Dynatrace/ufo/3dprint/ufo case sketch.png

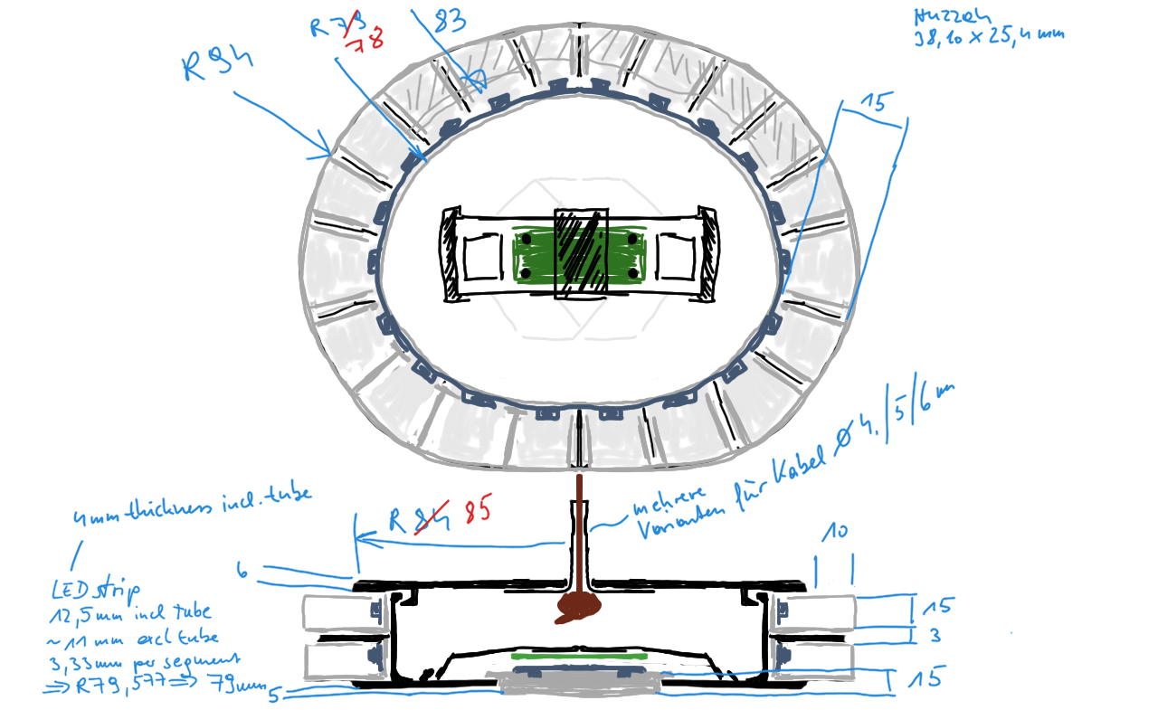
3dprint/ufo case sketch.png
