Dynatrace/ufo/howto/install neopixel library.png

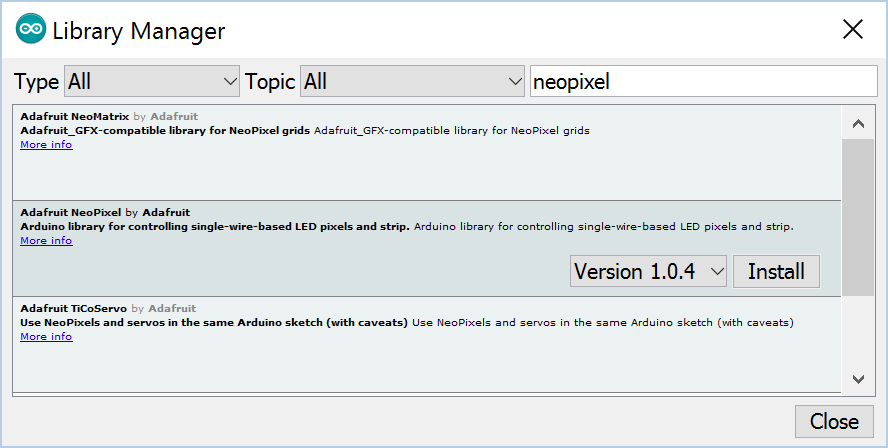
howto/install neopixel library.png
