Dynatrace/ufo/story/printed ufo lowres.png

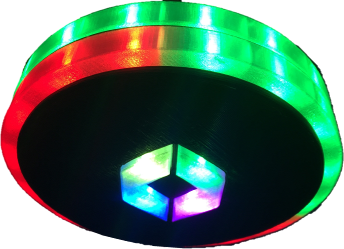
story/printed ufo lowres.png
