Dynatrace/ufo/story/printed ufo square.jpg

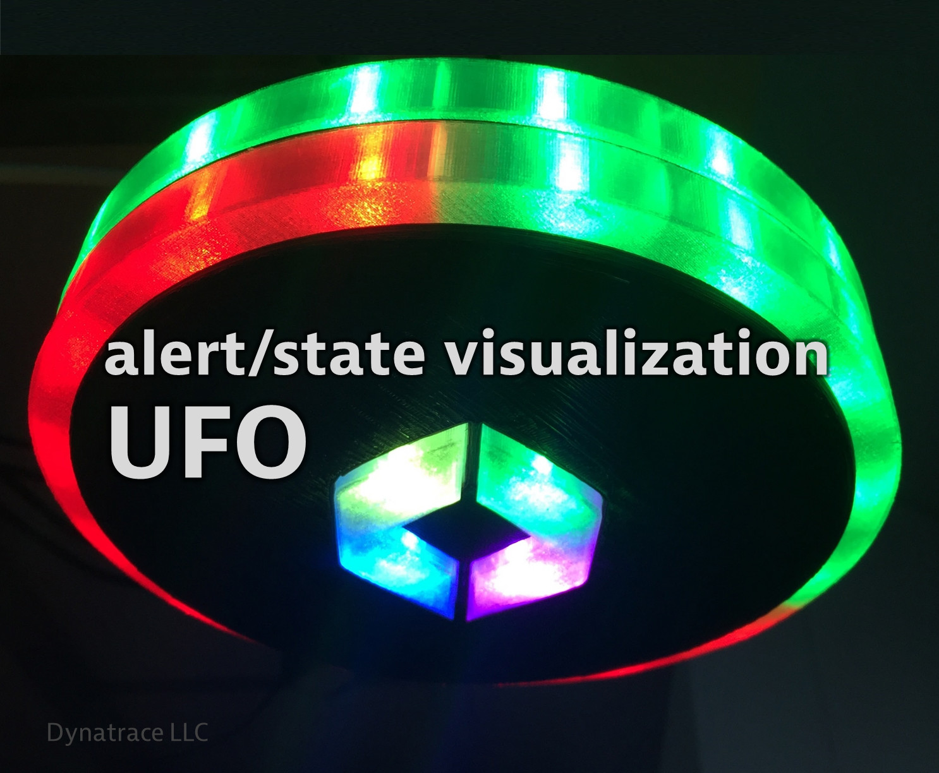
story/printed ufo square.jpg
