Dynatrace/ufo/story/printed ufo square.png

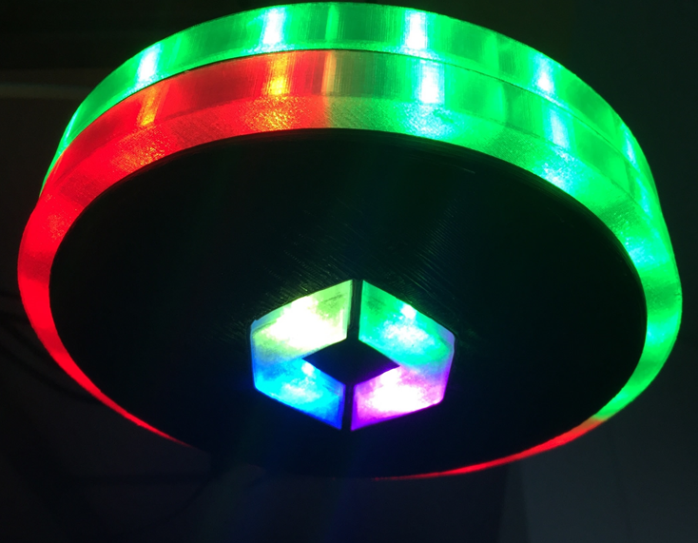
story/printed ufo square.png
