Dynatrace/ufo/WebContent.h

static const char PROGMEM index_html_gz[13780] = {
0x1f, 0x8b, 0x08, 0x08, 0x85, 0x08, 0x3c, 0x58, 0x02, 0xff, 0x69, 0x6e, 0x64, 0x65, 0x78, 0x2e, 0x68, 0x74, 0x6d, 0x6c, 0x00, 0xe5, 0x7d, 0x6b, 0x77, 0xdb, 0x38, 0x92, 0xe8, 0xe7, 0xec, 0x39, 0xfb, 0x1f, 0x68, 0xf6, 0xb6, 0x4d, 0xb6, 0x29, 0x5a, 0xf2, 0x23, 0x0f, 0x2a, 0x8c, 0xc7, 0x9d, 0xb8, 0x27, 
0xd9, 0x93, 0xd7, 0xc6, 0xee, 0x49, 0x66, 0xdd, 0xbe, 0x39, 0x14, 0x05, 0x49, 0xec, 0x50, 0xa4, 0x86, 0xa4, 0xfc, 0x68, 0x59, 0xfb, 0xdb, 0x6f, 0x55, 0x01, 0x20, 0x41, 0x12, 0x92, 0xed, 0x24, 0x33, 0xb3, 0x77, 0x6e, 0xa7, 0x8f, 0x45, 0x02, 0x85, 0x42, 0xa1, 0x50, 0xa8, 0x17, 0x40, 0xf2, 0xe9, 0xc6, 
0x8b, 0x77, 0xcf, 0x4f, 0xff, 0xfa, 0xfe, 0xd8, 0x98, 0x14, 0xd3, 0xf8, 0xd9, 0xbf, 0xff, 0xdb, 0x53, 0xf1, 0x8b, 0x57, 0x2c, 0x18, 0xc2, 0xd5, 0x83, 0xa7, 0x53, 0x56, 0x04, 0x46, 0x38, 0x09, 0xb2, 0x9c, 0x15, 0xbe, 0x39, 0x2f, 0x46, 0x9d, 0xc7, 0xa6, 0xb1, 0x53, 0x55, 0x25, 0xc1, 0x94, 0xf9, 0xe6, 
0x28, 0xcd, 0xa6, 0x41, 0xd1, 0x19, 0xb2, 0x82, 0x85, 0x45, 0x94, 0x26, 0xa6, 0x11, 0xa6, 0x49, 0xc1, 0x12, 0x68, 0x52, 0xb0, 0x98, 0xcd, 0x26, 0x69, 0xc2, 0xfc, 0x24, 0xd5, 0xb4, 0xbc, 0x88, 0xd8, 0xe5, 0x2c, 0xcd, 0x0a, 0xa5, 0xc5, 0x3c, 0x67, 0x59, 0x27, 0x0f, 0x83, 0x38, 0x18, 0xc4, 0xd8, 0xca, 
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
};
